joebmz98/Weasel-West-Coast-Synthesiser/src/WEASEL_FW/wavefolder.cpp

#include "wavefolder.h"
#include <utility/DaisySP/daisysp.h>
#include <math.h>

using namespace daisysp;

void Wavefolder::Init()
{
    gain_   = 1.0f;
    offset_ = 0.0f;
}

float Wavefolder::Process(float in)
{
    float ft, sgn;
    in += offset_;
    in *= gain_;
    ft  = floorf((in + 1.0f) * 0.5f);
    sgn = static_cast<int>(ft) % 2 == 0 ? 1.0f : -1.0f;
    return sgn * (in - 2.0f * ft);
}
